bhuvan21/OpenBox/tests/swordpiezotest/swordpiezotest.ino

unsigned long buttonPressedAt = 0;
const int BUTTON = A0;
bool buttonReleased = false;
byte buttonPrevState = 0;

#include <toneAC.h>

void setup() {
 pinMode(BUTTON,INPUT);
}

void loop() {

  int state = digitalRead(BUTTON);
  
  if (state != buttonPrevState) {
    if (state == HIGH) {
      buttonReleased = false;
      buttonPressedAt = millis();
    }
    else {
      buttonReleased = true;
    }
    buttonPrevState=state;
  }

  if (buttonReleased == true) {
    toneAC(2000);
    delay(1000);
    toneAC();
    
    buttonReleased=false;
    buttonPressedAt = 0;
  }
}
